wenfeng110402/HackPod/posters/drive-download-20251213T033350Z-1-001/Style Guide.png

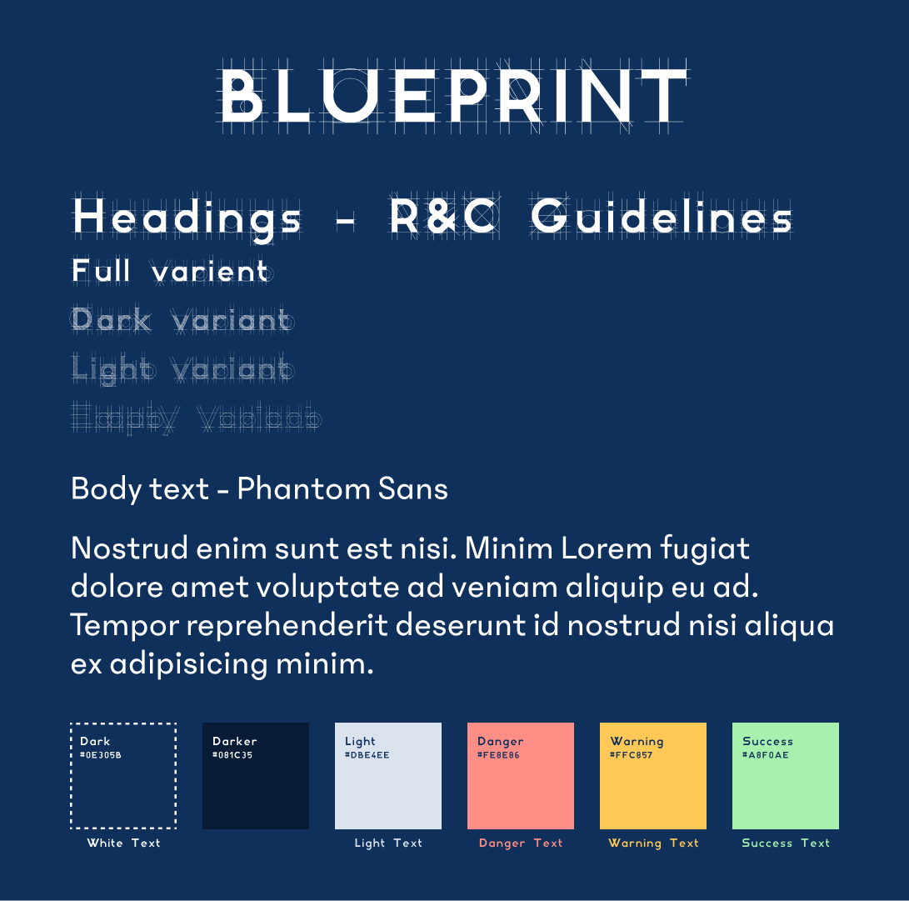
posters/drive-download-20251213T033350Z-1-001/Style Guide.png
